ea3iav/WiFi-Control-System-for-IC-PCR1000-using-ESP32/IMG_0535 2.PNG

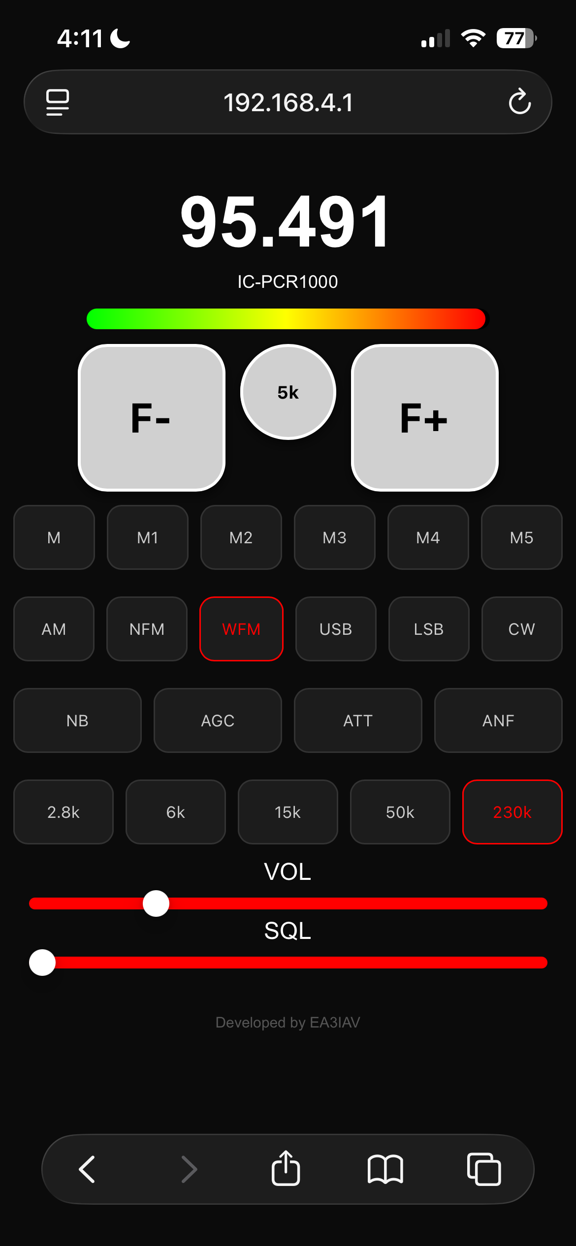
IMG_0535 2.PNG
