ea3iav/WiFi-Control-System-for-IC-PCR1000-using-ESP32/IMG_0536 3.PNG

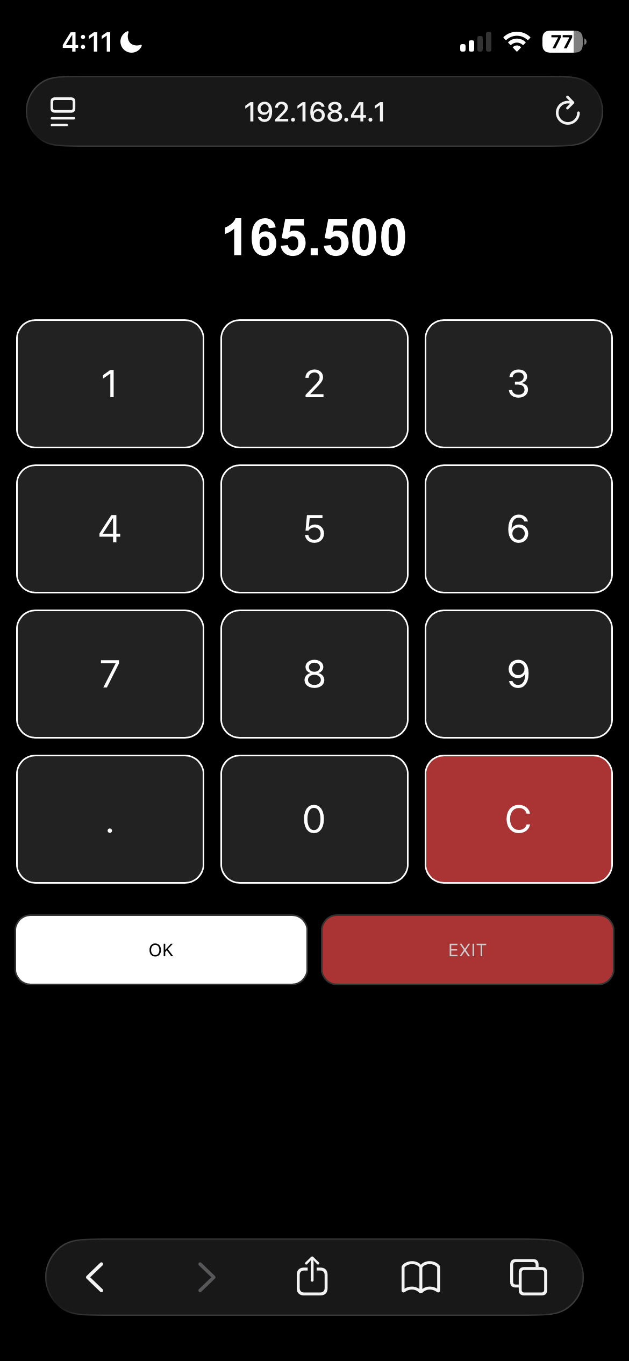
IMG_0536 3.PNG
